emeb/Cheep4/Firmware/osc0/wave_bank.h

const int16_t wave_bank[] = {
	/* index   0 */
	0x0000, 0x0324, 0x0648, 0x096b, 0x0c8c, 0x0fab, 0x12c8, 0x15e3, 
	0x18f9, 0x1c0c, 0x1f19, 0x2225, 0x2528, 0x2828, 0x2b1e, 0x2e10, 
	0x30fb, 0x33e0, 0x36ba, 0x398f, 0x3c57, 0x3f17, 0x41ce, 0x4479, 
	0x471e, 0x49b4, 0x4c3f, 0x4ec1, 0x5134, 0x539a, 0x55f6, 0x5842, 
	0x5a82, 0x5cb3, 0x5ed7, 0x60eb, 0x62f2, 0x64e7, 0x66ce, 0x68a6, 
	0x6a6c, 0x6c24, 0x6dc9, 0x6f5c, 0x70e2, 0x7255, 0x73b5, 0x7503, 
	0x7641, 0x776b, 0x7883, 0x7989, 0x7a7b, 0x7b5b, 0x7c2a, 0x7ce3, 
	0x7d8b, 0x7e1c, 0x7e9d, 0x7f0a, 0x7f61, 0x7fa7, 0x7fd8, 0x7ff7, 
	0x7fff, 0x7ff7, 0x7fd6, 0x7fa6, 0x7f62, 0x7f09, 0x7e9d, 0x7e1d, 
	0x7d8a, 0x7ce5, 0x7c2a, 0x7b5c, 0x7a7e, 0x7989, 0x7885, 0x776c, 
	0x7640, 0x7505, 0x73b5, 0x7254, 0x70e3, 0x6f5d, 0x6dc9, 0x6c24, 
	0x6a6e, 0x68a5, 0x66ce, 0x64e9, 0x62f2, 0x60ea, 0x5ed7, 0x5cb2, 
	0x5a82, 0x5842, 0x55f6, 0x539a, 0x5132, 0x4ec0, 0x4c3f, 0x49b5, 
	0x471c, 0x447b, 0x41ce, 0x3f19, 0x3c55, 0x398e, 0x36ba, 0x33e0, 
	0x30fa, 0x2e12, 0x2b20, 0x2826, 0x2527, 0x2224, 0x1f1b, 0x1c09, 
	0x18f9, 0x15e3, 0x12c8, 0x0faa, 0x0c8c, 0x096a, 0x0647, 0x0323, 
	0x0000, 0xfcdd, 0xf9b8, 0xf696, 0xf374, 0xf055, 0xed38, 0xea1d, 
	0xe709, 0xe3f4, 0xe0e6, 0xddde, 0xdad8, 0xd7da, 0xd4e0, 0xd1ef, 
	0xcf04, 0xcc22, 0xc945, 0xc674, 0xc3a9, 0xc0e9, 0xbe32, 0xbb85, 
	0xb8e5, 0xb64b, 0xb3c1, 0xb13f, 0xaecf, 0xac65, 0xaa09, 0xa7be, 
	0xa57f, 0xa34c, 0xa129, 0x9f14, 0x9d0f, 0x9b18, 0x9932, 0x9759, 
	0x9592, 0x93de, 0x9236, 0x90a2, 0x8f1e, 0x8dab, 0x8c4b, 0x8afa, 
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
	0x7ffd, 0x7ffd, 0x7ffd, 0x7ffc, 0x7fff, 0x7ffe, 0x7ffd, 0x7ffd, 
	0x7ffd, 0x7ffc, 0x7ffd, 0x7ffe, 0x7ffe, 0x7ffd, 0x7fff, 0x7ffc, 
	0x7ffe, 0x7ffd, 0x7ffd, 0x7ffe, 0x7ffd, 0x7ffe, 0x7ffe, 0x7ffd, 
	0x7ffd, 0x7ffd, 0x7ffc, 0x7ffc, 0x7ffd, 0x7fff, 0x7ffd, 0x7ffe,
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
