emeb/Cheep4/Firmware/common/cyclesleep.c

/*
 * cyclesleep.c - zyp's cycle counter sleep routines
 * 09-05-15 E. Brombaugh - updated for F7 and HAL
 * 03-20-17 E. Brombaugh - fixed wrap bug, update comments
 * 11-08-24 E. Brombaugh - updated for H5
 * 04-02-26 E. Brombaugh - updated for U3
 * 04-12-26 E. Brombaugh - updated for C5
 */
 
#include "cyclesleep.h"

uint32_t DelayCyc1s; 
uint32_t s_tot, act_cyc, tot_cyc;

/*
 * turn on cycle counter
 */
void cyccnt_enable()
{
    /* Enable TRC */
    DCB->DEMCR |=  CoreDebug_DEMCR_TRCENA_Msk;
	
    /* Enable cycle counter */
    DWT->CTRL |=  DWT_CTRL_CYCCNTENA_Msk;
	
	/* get sysclk freq for computing delay */
	DelayCyc1s = HAL_RCC_GetSYSCLKFreq();
}

/*
 * compute goal for cycle counter based on desired delay in cycles
 */
uint32_t cyclegoal(uint32_t cycles)
{
	return cycles + DWT->CYCCNT;
}

/*
 * compute goal for cycle counter based on desired delay in milliseconds
 */
uint32_t cyclegoal_ms(uint32_t ms)
{
	int64_t inc = ms*(DelayCyc1s/1000);
	int64_t cnt = DWT->CYCCNT;
	
	return cnt + inc;
}

/*
 * return TRUE if goal is reached
 */
uint32_t cyclecheck(uint32_t goal)
{
    /**************************************************/
    /* DANGER WILL ROBINSON!                          */
    /* the following syntax is CRUCIAL to ensuring    */
    /* that this test doesn't have a wrap bug         */
    /**************************************************/
	return ((int32_t)(DWT->CYCCNT - goal) < 0);
}

/*
 * return microseconds for cycles
 */
uint32_t cycle2us(uint32_t cycles)
{
	return cycles / (DelayCyc1s/1000000);
}

/*
 * sleep for a certain number of cycles
 */
void cyclesleep(uint32_t cycles)
{
    uint32_t goal = cyclegoal(cycles);
    
    while(cyclecheck(goal));
}

/*
 * sleep for a certain number of milliseconds
 */
void delay(uint32_t ms)
{
	cyclesleep(ms*(DelayCyc1s/1000));
}

/*
 * sleep for a certain number of microseconds
 */
void delay_us(uint32_t us)
{
	cyclesleep(us*(DelayCyc1s/1000000));
}

/*
 * called at start of routine to be measured
 */
void start_meas(void)
{
	/* grab current cycle count & measure total cycles */
	uint32_t curr_cyc = DWT->CYCCNT;
	tot_cyc = curr_cyc - s_tot;
	s_tot = curr_cyc;

}

/*
 * called at end of routine to be measured
 */
void end_meas(void)
{
	/* grab current cycle count and measure active cycles */
	uint32_t curr_cyc = DWT->CYCCNT;
	act_cyc = curr_cyc - s_tot;
}

/*
 * return the measurement results
 */
void get_meas(uint32_t *act, uint32_t *tot)
{
	*act = act_cyc;
	*tot = tot_cyc;
}
